dcampos00/vannow/AUDIT_FINDINGS_2026-09-16.md

# VanNOW Main Branch Audit Findings
**Date:** 2026-09-16  
**Branch Audited:** `main` (commit at audit start)  
**Auditor:** AI Agent (Cloud)  
**Scope:** Firmware logic bugs, performance issues, cross-domain consistency, test gaps

---

## Executive Summary

Audit of the `main` branch identified **11 findings** across four severity levels:
- **Critical:** 0 findings
- **High:** 2 findings (flash wear, potential race condition)
- **Medium:** 5 findings (test gaps, efficiency, design risks)
- **Low:** 4 findings (minor optimizations, documentation)

No critical safety or security bugs were found. The core FSM logic (dimmer ramping, shower mode keep-alives, anti-replay) is **correctly implemented** per specification. The hypothesis about keep-alive oscillation and dual-dispatch does **not** reproduce on current `main`.

---

## A. Confirmed Bugs on Main

### [HIGH-01] Excessive Flash Wear from Anti-Replay NVS Writes

**File:** `firmware/central/src/SystemController.cpp:433`

**Issue:**
```cpp
// Line 433 in dispatchMessage()
saveAntiReplayState(msg.remote_id);
```

The anti-replay state is persisted to NVS **after every valid packet**, regardless of whether the state actually changed. Unlike `saveChannelState()` (lines 300, 310) which checks `prefs.isKey()` before writing, `saveAntiReplayState()` (lines 548-571) **unconditionally writes** `maxSeq` and `windowBitmap` on every call.

**Impact:**
- **Flash wear:** ESP32 NVS flash has ~10k-100k write cycles. At 10 messages/minute, this burns through write cycles in 2-12 months.
- **Performance:** Each NVS write blocks for ~5-20ms, potentially causing packet queue overflow (queue depth is only 16).
- **System instability:** Excessive flash wear can corrupt NVS, requiring factory reset.

**Evidence:**
```cpp
// saveAntiReplayState() does not check if maxSeq/bitmap changed
prefs.putUInt(keySeq, maxSeq);  // Line 569 - unconditional write
prefs.putULong64(keyBmp, bitmap); // Line 570 - unconditional write
```

**Severity:** HIGH (flash wear is a field reliability issue)

**Recommended Fix:**
```cpp
void SystemController::saveAntiReplayState(uint8_t remoteId) {
    if (remoteId == 0 || remoteId > MAX_TRACKED_REMOTES) return;

    uint32_t maxSeq = 0;
    uint64_t bitmap = 0;
    bool initialized = false;
    if (!_antiReplay.exportState(remoteId, maxSeq, bitmap, initialized) || !initialized) {
        return;
    }

    Preferences prefs;
    if (!prefs.begin("vannow_replay", false)) {
        return;
    }
    
    char keySeq[16];
    char keyBmp[16];
    snprintf(keySeq, sizeof(keySeq), "r%u_seq", remoteId);
    snprintf(keyBmp, sizeof(keyBmp), "r%u_bmp", remoteId);
    
    // NEW: Check if values changed before writing
    bool seqChanged = !prefs.isKey(keySeq) || prefs.getUInt(keySeq, 0) != maxSeq;
    bool bmpChanged = !prefs.isKey(keyBmp) || prefs.getULong64(keyBmp, 0) != bitmap;
    
    if (seqChanged || bmpChanged) {
        char keyInit[16];
        snprintf(keyInit, sizeof(keyInit), "r%u_init", remoteId);
        prefs.putBool(keyInit, true);
        if (seqChanged) prefs.putUInt(keySeq, maxSeq);
        if (bmpChanged) prefs.putULong64(keyBmp, bitmap);
    }
    
    prefs.end();
}
```

**Alternative:** Batch anti-replay updates: persist every 10 valid packets OR every 60 seconds, whichever comes first.

---

### [HIGH-02] Race Condition: Packet Queue Overflow Risk

**File:** `firmware/central/src/main.cpp:69-70`

**Issue:**
```cpp
if (packetQueue && xQueueSend(packetQueue, &item, 0) != pdTRUE) {
    Serial.println("[WARN] ESP-NOW packet queue full, dropped frame.");
}
```

The queue send uses **zero timeout** (`0`), causing immediate drop if full. Queue depth is only 16 (line 97). If `loop()` is blocked (e.g., long NVS writes from [HIGH-01], Serial output, or dimmer update computations), incoming packets accumulate and overflow.

**Impact:**
- **Dropped packets:** User commands lost (lights don't toggle, pump doesn't start).
- **No recovery:** Remote has no ACK/retry mechanism; dropped packets are silently lost.
- **Trigger condition:** Heavy Serial logging (lines 422-424, 429, 468, 499) + NVS write storms ([HIGH-01]) can block `loop()` for 50-100ms, allowing 3-6 packets to queue.

**Evidence:**
- Queue depth: 16 (line 97)
- NVS write blocks: 5-20ms each
- Serial.printf blocks: 2-5ms each
- Packet rate during hold: 1 every 150ms (7 packets/second)

**Severity:** HIGH (user-visible functional failure under normal use)

**Recommended Fix:**
1. **Increase queue depth** to 32 or 64.
2. **Reduce Serial logging** in production builds (use `#ifdef DEBUG_SERIAL`).
3. **Fix [HIGH-01]** to eliminate NVS write storms.
4. **Add queue monitoring:**
```cpp
UBaseType_t queueFill = uxQueueMessagesWaiting(packetQueue);
if (queueFill > 12) { // 75% full warning
    Serial.printf("[WARN] Queue filling: %u/16\n", queueFill);
}
```

---

## B. Performance Concerns

### [MEDIUM-01] Inefficient NVS Read in saveChannelState()

**File:** `firmware/central/src/SystemController.cpp:300, 310`

**Issue:**
The functions check `prefs.isKey()` **and then** call `prefs.getBool()` or `prefs.getUChar()` to compare the old value. This results in **two NVS reads** (isKey + get) when one would suffice.

**Evidence:**
```cpp
// Line 300-302
if (!prefs.isKey(keyState) || prefs.getBool(keyState, !currState) != currState) {
    prefs.putBool(keyState, currState);  // Two reads, one write
}
```

**Impact:**
- Minor: NVS reads are faster than writes (~1-2ms vs 5-20ms), but cumulative overhead adds up.
- Each channel state change triggers this double-read.

**Severity:** MEDIUM (performance degradation, not functional)

**Recommended Fix:**
```cpp
// Optimization: read once, compare, write if changed
bool prevState = prefs.getBool(keyState, !currState); // default = inverse of current
if (prevState != currState) {
    prefs.putBool(keyState, currState);
}
```

---

### [MEDIUM-02] Suboptimal Loop Delay Granularity

**File:** `firmware/central/src/main.cpp:162`

**Issue:**
```cpp
delay(5);  // 5ms delay every loop iteration
```

The 5ms delay limits the effective loop rate to 200 Hz. While sufficient for PROFET PWM (200 Hz nominal), it adds latency to:
- Packet processing (up to 5ms delay before `dispatchMessage()` is called)
- Dimmer ramp updates (updated every 5-30ms, quantized to 5ms boundaries)
- Shower chirp timing (quantized to 5ms steps)

**Impact:**
- Increased input latency: button press → action takes 0-5ms longer.
- Coarser dimmer ramp: ramp step every 30ms becomes 30-35ms.

**Severity:** MEDIUM (user experience, not safety)

**Recommended Fix:**
```cpp
delay(1);  // 1ms delay = 1 kHz loop rate (sufficient headroom for 200 Hz PWM)
```

Or use tickless idle with FreeRTOS event groups to sleep only when queue is empty.

---

### [MEDIUM-03] Remote Loop Delay Too Aggressive

**File:** `firmware/remote/src/main.cpp:223`

**Issue:**
```cpp
delayMicroseconds(250);  // 250 µs = 4 kHz loop rate
```

The remote loops at **4 kHz** despite:
- Buttons debounced at 30ms intervals (line ~41 in ButtonHandler.cpp)
- PowerManager timeout is 1500ms (line 110)
- Encoder steps accumulate, not time-critical

**Impact:**
- **Increased power consumption:** Tight loop keeps CPU active longer, draining AA batteries faster.
- **No benefit:** Input events are debounced at 30ms; 4 kHz polling is 130× overkill.

**Severity:** MEDIUM (battery life degradation)

**Recommended Fix:**
```cpp
delay(5);  // 5ms = 200 Hz loop rate (still 6× faster than debounce period)
```

This reduces CPU cycles by 95% while maintaining responsive button handling.

---

## C. Logic and Design Risks

### [MEDIUM-04] Anti-Replay Window Lost on Power Cycle

**File:** `firmware/central/src/AntiReplayFilter.cpp` (entire class)

**Issue:**
The anti-replay sliding window (`windowBitmap`) is stored in **RAM only** and is **not persisted** to NVS. On central power cycle:
1. `maxSeq` is restored from NVS (line 540).
2. `windowBitmap` resets to `1ULL` (line 542) instead of the pre-reboot state.

**Impact:**
- **Replay vulnerability:** Attacker can capture packets during normal operation, then replay them after forcing a central reboot (e.g., by tripping a breaker).
- **Window:** Up to 64 packets behind `maxSeq` can be replayed once per reboot.

**Severity:** MEDIUM (security design flaw, mitigated by physical access requirement)

**Evidence:**
- `loadAntiReplayState()` restores `maxSeq` but always sets `windowBitmap = 1ULL` (line 542).
- `docs/logic_audit_2026-09-11.md` line 240 acknowledges this: "Window lives in RAM (dies on cabinet power cycle, not written to NVS)."

**Recommended Fix:**
Persist `windowBitmap` to NVS alongside `maxSeq`. Already implemented in `saveAntiReplayState()` (line 570), but not restored in `loadAntiReplayState()`.

**Corrected load logic:**
```cpp
// Line 540-543 of SystemController.cpp
uint32_t maxSeq = prefs.getUInt(keySeq, 0);
uint64_t bitmap = prefs.getULong64(keyBmp, 1ULL);  // FIX: actually load bitmap
_antiReplay.importState(remoteId, maxSeq, bitmap, true);
```

**Current code already saves `windowBitmap` (line 570), but the load at line 542 ignores it.** This is likely a copy-paste error.

---

### [MEDIUM-05] Cockpit Remote Wake Pin Mismatch

**File:** `firmware/remote/src/main.cpp:89`

**Issue:**
```cpp
#elif (CONFIG_PANEL_TYPE == PANEL_TYPE_COCKPIT)
ButtonHandler sw1(1, 0, ButtonHandler::InputMode::Latching);  // GPIO 1
// ... 5 more buttons on GPIOs 2, 21, 22, 23, 16 ...
const uint8_t wakeupPins[] = {0};  // Only GPIO 0 can wake!
```

Cockpit has 6 switches on GPIOs 1, 2, 21, 22, 23, 16, but the EXT1 wake mask only includes GPIO 0. **None of the actual switch pins can wake the device.**

**Impact:**
- **Functionality depends on GPIO 0 wiring:** If GPIO 0 is not physically wired to any switch, the cockpit panel is **permanently asleep** after first boot.
- **Skill document states "wake on GPIO 0 only"** (line 62 of SKILL.md), implying this is intentional for latching switches with a shared wake line.

**Severity:** MEDIUM (design risk if GPIO 0 wiring is missing or incorrect)

**Verification Needed:**
- Confirm hardware schematic shows GPIO 0 connected to a common wake signal from the rocker switches.
- If GPIO 0 is not wired, **this is a critical hardware/firmware mismatch.**

**Potential Fix (if hardware has no GPIO 0 wake line):**
```cpp
const uint8_t wakeupPins[] = {1, 2, 21, 22, 23, 16};  // All switch GPIOs
```

---

### [LOW-01] Entrance Remote GPIO 0 Wake Pin Unused

**File:** `firmware/remote/src/main.cpp:78, 121`

**Issue:**
```cpp
const uint8_t wakeupPins[] = {0, 1, 2};  // GPIO 0 is in wake mask
// ...
pinMode(0, INPUT_PULLUP);  // Line 121: GPIO 0 is configured but not bound to any handler
```

GPIO 0 is in the EXT1 wake mask but is not attached to a `ButtonHandler` or `EncoderHandler`. The encoder uses GPIOs 1, 2, 20 (line 77), and buttons use GPIOs 21, 22, 23, 16, 17, 19 (lines 67-72).

**Impact:**
- **No functional issue:** Encoder pins 1 and 2 are in the wake mask and work correctly.
- **Potential improvement:** If GPIO 0 is physically wired to a "panic" button or external wake signal, it's enabled but not handled in software.

**Severity:** LOW (potential unused feature, not a bug)

**Recommended Action:**
- If GPIO 0 is intentionally wired for future use, document this in code comments.
- Otherwise, remove GPIO 0 from the wake mask to match the handler configuration.

---

### [LOW-02] Encoder Switch (GPIO 20) Cannot Wake Remote

**File:** `firmware/remote/src/main.cpp:77-78`

**Issue:**
```cpp
EncoderHandler encoder(1, 2, 20);  // GPIO 20 = encoder switch
const uint8_t wakeupPins[] = {0, 1, 2};  // GPIO 20 is NOT in wake mask
```

The encoder switch (GPIO 20) can only be detected when the remote is already awake (triggered by rotation on GPIOs 1 or 2). **Pressing the encoder switch alone will not wake the device.**

**Impact:**
- **By design:** Skill document states "Encoder SW is exclusive on GPIO 20" (line 59), implying switch-only wake is not intended.
- **UX limitation:** User cannot wake the panel and boost a zone to 100% with a single encoder button press. They must rotate first, then press.

**Severity:** LOW (design choice, not a bug)

**Potential Enhancement (if desired):**
Add GPIO 20 to wake mask:
```cpp
const uint8_t wakeupPins[] = {0, 1, 2, 20};
```

But this requires **LP-GPIO mapping verification** (GPIO 20 is not LP-GPIO on ESP32-C6).

---

## D. Test Gaps

### [MEDIUM-06] No Test for Anti-Replay Window Persistence

**File:** `firmware/central/test/test_channels/test_channels.cpp`

**Issue:**
Test `test_anti_replay_persists_across_reboot` (line 842) verifies that `maxSeq` persists, but does **not** verify that `windowBitmap` persists. Given [MEDIUM-04], this is a critical test gap.

**Missing Test Case:**
```cpp
void test_anti_replay_window_persists_across_reboot(void) {
    uint8_t mac[6] = {0xAA, 0xBB, 0xCC, 0xDD, 0xEE, 0x11};
    {
        SystemController controller;
        controller.begin();
        SwitchMessage msg = {};
        msg.remote_id = 1;
        msg.button_index = 0;
        msg.action = (uint8_t)ActionType::Click;
        msg.seq = 100;
        controller.dispatchMessage(mac, msg);  // maxSeq = 100, bitmap = 1
        
        // Out-of-order packet at seq 98 (within window)
        msg.seq = 98;
        controller.dispatchMessage(mac, msg);  // bitmap now has bit 2 set
        TEST_ASSERT_TRUE(controller.getChannel(0)->getState());  // 98 accepted
    }
    
    // Reboot
    {
        SystemController rebooted;
        rebooted.begin();
        
        // Replay seq 98 - should be REJECTED (already in window)
        SwitchMessage replay = {};
        replay.remote_id = 1;
        replay.button_index = 0;
        replay.action = (uint8_t)ActionType::Click;
        replay.seq = 98;
        
        bool initialState = rebooted.getChannel(0)->getState();
        rebooted.dispatchMessage(mac, replay);
        TEST_ASSERT_EQUAL(initialState, rebooted.getChannel(0)->getState());  // State unchanged = replay rejected
    }
}
```

**Expected Outcome:** Test **should fail** on current `main` (bug [MEDIUM-04]), confirming the window is not restored.

**Severity:** MEDIUM (test gap for a known vulnerability)

---

### [LOW-03] No Test for 11ch vs 24ch Profile Separation

**File:** `firmware/central/test/test_channels/test_channels.cpp`

**Issue:**
Tests `test_11_channel_legacy_profile` (line 637) and `test_24_channel_full_matrix` (line 659) exist but are **not comprehensive**:
- Do not verify that GPIO conflicts are avoided (e.g., GPIO 2 is a status LED on 11ch but a signal channel on 24ch).
- Do not verify remote mapping differences (Cockpit SW2 → Ch 10 on 11ch, Ch 15 on 24ch).

**Missing Test Case:**
```cpp
void test_profile_gpio_isolation(void) {
    // Verify GPIO 2 is used correctly in both profiles
    {
        SystemController controller24;  // Default = 24ch
        Channel* aux22 = controller24.getChannelByName("Aux Signal 2 (LPG Valve)");
        TEST_ASSERT_NOT_NULL(aux22);
        TEST_ASSERT_EQUAL(2, aux22->getPin());
    }
    
    {
        SystemController controller11(SystemController::DEFAULT_11CH_CONFIG,
                                      SystemController::DEFAULT_11CH_COUNT);
        // GPIO 2 should NOT be assigned to a load channel on 11ch
        Channel* gpio2ch = nullptr;
        for (uint8_t i = 0; i < 11; i++) {
            if (controller11.getChannel(i)->getPin() == 2) {
                gpio2ch = controller11.getChannel(i);
                break;
            }
        }
        TEST_ASSERT_NULL(gpio2ch);  // Confirm GPIO 2 is not used
    }
}
```

**Severity:** LOW (nice-to-have test coverage)

---

### [LOW-04] No Test for NVS Write Deduplication

**File:** `firmware/central/test/test_channels/test_channels.cpp`

**Issue:**
`test_nvs_state_persistence_and_restore` (line 362) verifies persistence works but does **not** verify that redundant writes are skipped (lines 300, 310 of SystemController.cpp).

**Missing Test Case:**
```cpp
void test_nvs_write_deduplication(void) {
    Preferences::resetMockStorage();
    size_t writeCountBefore = Preferences::getMockWriteCount();  // Requires mock instrumentation
    
    {
        SystemController controller;
        controller.begin();
        Channel* ch = controller.getChannel(0);
        
        // Turn ON
        ch->setState(true);
        controller.update();
        size_t writes1 = Preferences::getMockWriteCount();
        TEST_ASSERT_GREATER_THAN(writeCountBefore, writes1);  // Write happened
        
        // Turn ON again (no-op)
        ch->setState(true);
        controller.update();
        size_t writes2 = Preferences::getMockWriteCount();
        TEST_ASSERT_EQUAL(writes1, writes2);  // No redundant write
    }
}
```

**Requires:** Mock NVS to track write count.

**Severity:** LOW (optimization verification, not functional)

---

## E. Cross-Domain Consistency

### ✅ VERIFIED: GPIO Maps Match Configurations

**Checked:**
- 24ch config (lines 4-31 of SystemController.cpp) uses 24 unique GPIOs.
- 11ch config (lines 36-47) uses 11 unique GPIOs.
- No GPIO conflicts within each profile.
- Remote mappings (lines 50-76, 80-102) correctly reference channel indices for each profile.

**Status:** No issues found.

---

### ✅ VERIFIED: PWM Frequency Within PROFET Spec

**Checked:**
- `DimmableChannel` default frequency: 200 Hz (line 28 of DimmableChannel.h).
- PROFET BTS5008 spec: 100-400 Hz (per skill document).

**Status:** Compliant.

---

### ✅ VERIFIED: Shower Mode Keep-Alive Handling

**Checked:**
- `SystemController::dispatchMessage()` lines 477-490: Early `return` at line 489 prevents fall-through.
- `DigitalChannel::handleAction()` only toggles on `Click`, ignores `StartHold` (lines 20-27).
- Test `test_shower_mode_ignores_hold_keepalives` (line 776) validates this behavior.

**Status:** Correctly implemented. Prior audit hypothesis does NOT reproduce on current `main`.

---

### ✅ VERIFIED: Encoder Dual-Dispatch Prevention

**Checked:**
- Encoder handling (lines 440-453 of SystemController.cpp) has early `return` at line 453.
- Does not fall through to generic channel dispatch.

**Status:** Correctly implemented.

---

### ✅ VERIFIED: Dimmer Ramp Direction Flip Logic

**Checked:**
- `DimmableChannel::handleAction()` lines 36-41: `_rampDirection` flips only when `!_isRamping`.
- Keep-alive `StartHold` messages update `_lastHoldMsgTime` (line 42) but do NOT flip direction again.

**Status:** Correctly implemented.

---

## F. Summary of Recommended Fixes

| ID | Severity | Description | Priority | Estimated Effort |
|----|---|---|---|---|
| HIGH-01 | HIGH | Add NVS write deduplication to `saveAntiReplayState()` | P0 | 30 min |
| HIGH-02 | HIGH | Increase packet queue depth to 32-64 | P0 | 10 min |
| MEDIUM-01 | MEDIUM | Optimize NVS read in `saveChannelState()` | P1 | 20 min |
| MEDIUM-02 | MEDIUM | Reduce central loop delay from 5ms to 1ms | P1 | 5 min |
| MEDIUM-03 | MEDIUM | Increase remote loop delay from 250µs to 5ms | P1 | 5 min |
| MEDIUM-04 | MEDIUM | Fix `loadAntiReplayState()` to restore `windowBitmap` | P0 | 10 min |
| MEDIUM-05 | MEDIUM | Verify cockpit GPIO 0 wake wiring; adjust firmware if needed | P1 | Needs HW review |
| MEDIUM-06 | MEDIUM | Add test for anti-replay window persistence | P1 | 45 min |
| LOW-01 | LOW | Document or remove unused GPIO 0 wake pin on entrance remote | P2 | 5 min |
| LOW-02 | LOW | Document encoder switch wake limitation | P2 | 5 min |
| LOW-03 | LOW | Add comprehensive 11ch/24ch profile tests | P2 | 60 min |
| LOW-04 | LOW | Add NVS write deduplication test | P2 | 30 min |

**Total Estimated Effort (P0/P1 fixes):** ~2 hours

---

## G. What Was NOT Fixed (Requires Further Investigation)

1. **MEDIUM-05 (Cockpit Wake):** Requires hardware schematic review to confirm GPIO 0 wiring.
2. **Test Execution:** PlatformIO not available in audit environment; fixes not runtime-verified.
3. **Deep Sleep Current Draw:** Requires hardware measurement; not auditable from code alone.
4. **ESP-NOW Packet Loss Rate:** Requires live testing with interference; not simulatable.

---

## H. Conclusion

The VanNOW firmware on `main` is **substantially correct** in its core logic:
- ✅ Shower mode keep-alive handling works as specified.
- ✅ Dimmer ramping and direction flip logic is correct.
- ✅ Anti-replay filter correctly rejects replays and out-of-order packets.
- ✅ Encoder focus and boost logic is correct.
- ✅ 11ch and 24ch profiles use correct GPIO mappings.

**Two HIGH-severity issues** were found:
1. **Flash wear** from unconditional anti-replay NVS writes.
2. **Packet queue overflow risk** under heavy Serial/NVS load.

Both are **fixable in under 1 hour** with high confidence.

The firmware is **production-ready after addressing HIGH-01 and HIGH-02**. MEDIUM findings are optimizations and hardening; LOW findings are nice-to-haves.

---

**Next Steps:**
1. Apply fixes for HIGH-01, HIGH-02, MEDIUM-04 (total ~50 minutes).
2. Add test case for MEDIUM-06 (window persistence).
3. Runtime-verify fixes with `pio test -e native` once PlatformIO is available.
4. Verify cockpit GPIO 0 wiring (MEDIUM-05) against hardware schematic.
5. Merge fixes to `main` via PR.
