dcampos00/vannow/hardware/central-pcb/renders/modular_bottom.png

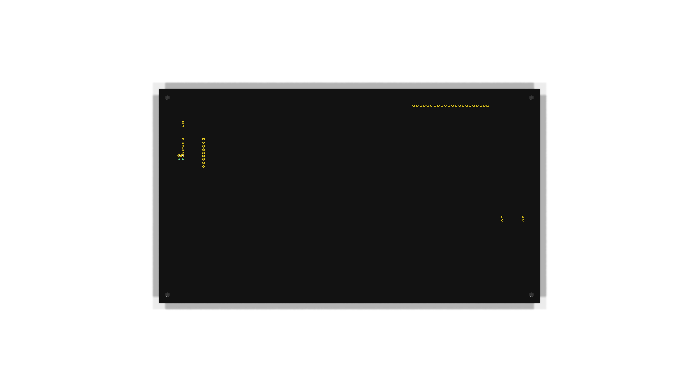
hardware/central-pcb/renders/modular_bottom.png
