dcampos00/vannow/hardware/central-pcb/renders/modular_silkscreen.png

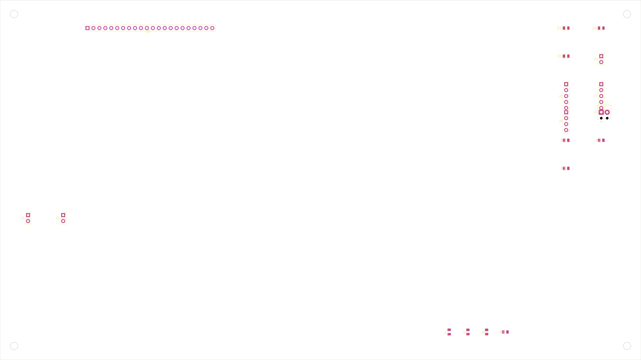
hardware/central-pcb/renders/modular_silkscreen.png
