dcampos00/vannow/hardware/central-pcb/renders/modular_top.png

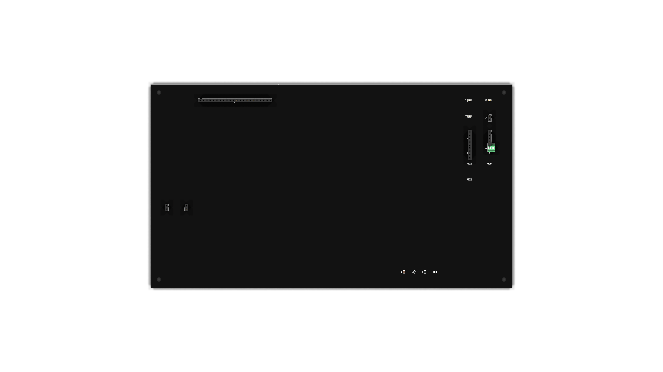
hardware/central-pcb/renders/modular_top.png
