dcampos00/vannow/hardware/central-pcb/renders/profet_24ch/profet_24ch_isometric.png

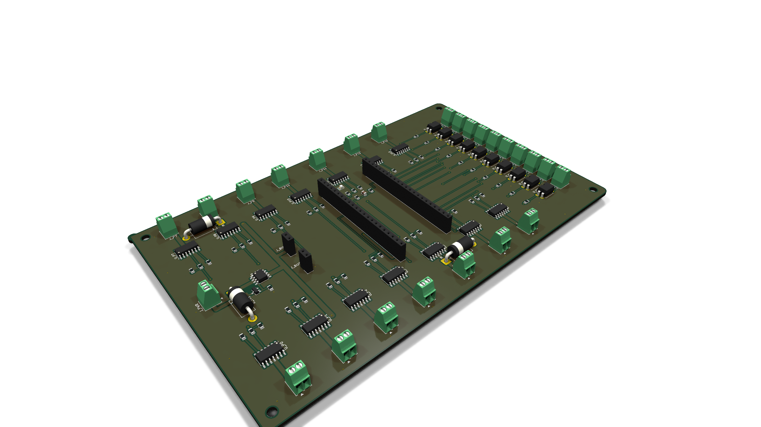
hardware/central-pcb/renders/profet_24ch/profet_24ch_isometric.png
