dcampos00/vannow/hardware/central-pcb/renders/profet_24ch/profet_24ch_top.png

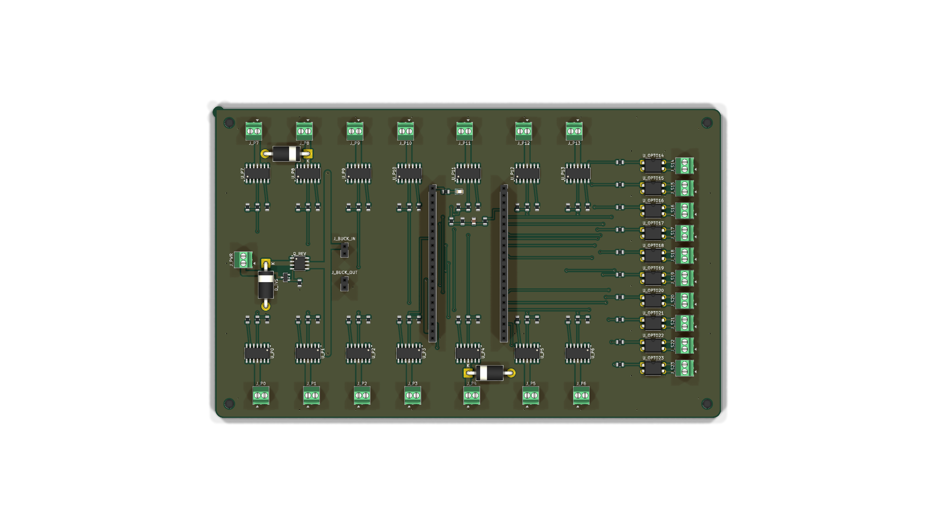
hardware/central-pcb/renders/profet_24ch/profet_24ch_top.png
