dcampos00/vannow/hardware/central-pcb/renders/profet_bottom.png

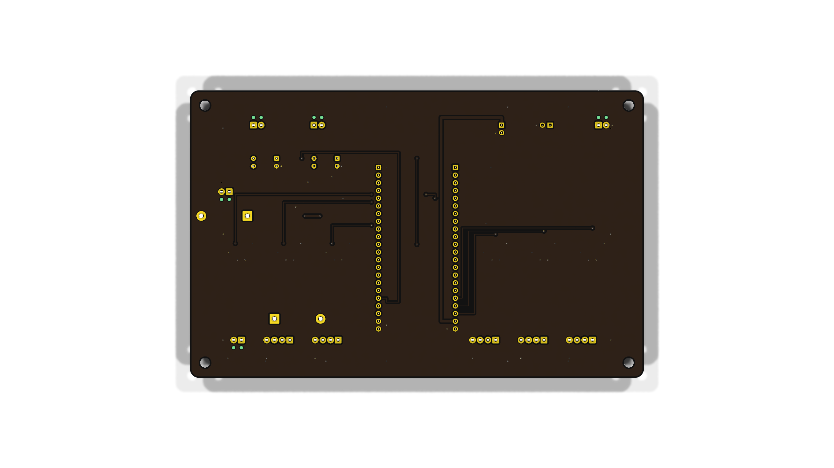
hardware/central-pcb/renders/profet_bottom.png
