dcampos00/vannow/hardware/cockpit-pcb/renders/cockpit_bottom.png

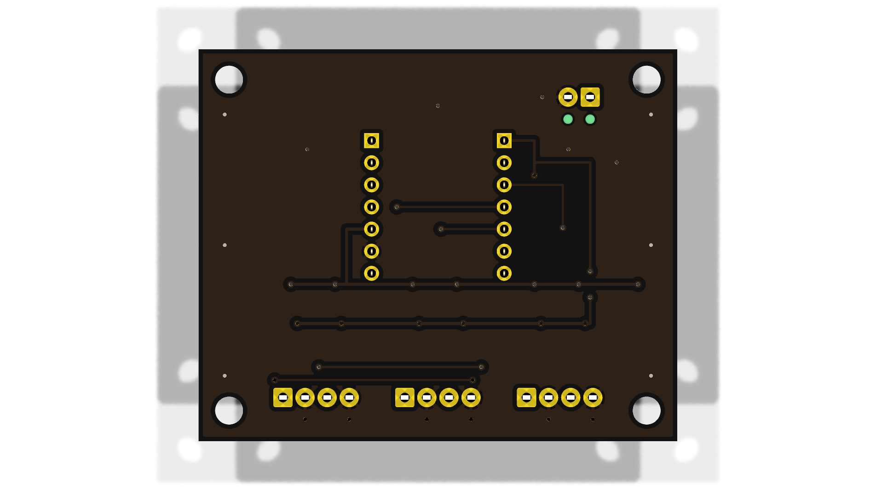
hardware/cockpit-pcb/renders/cockpit_bottom.png
