dcampos00/vannow/hardware/cockpit-pcb/renders/cockpit_isometric.png

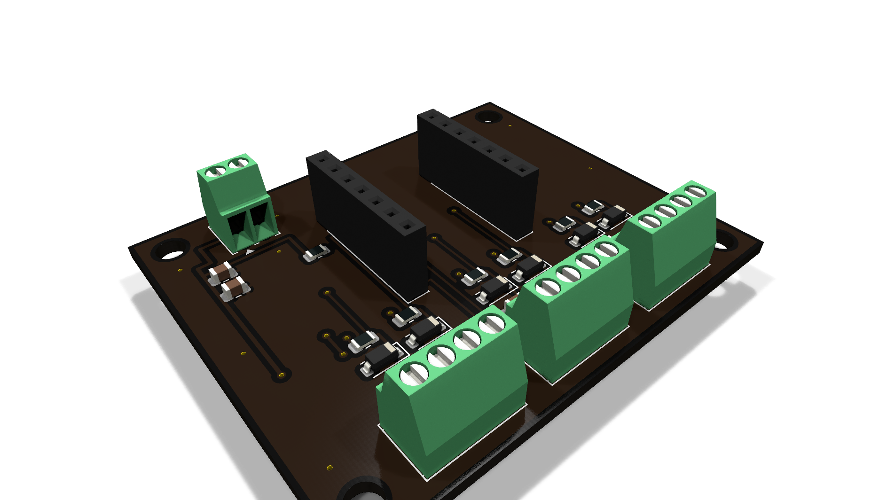
hardware/cockpit-pcb/renders/cockpit_isometric.png
