dcampos00/vannow/hardware/cockpit-pcb/renders/cockpit_top.png

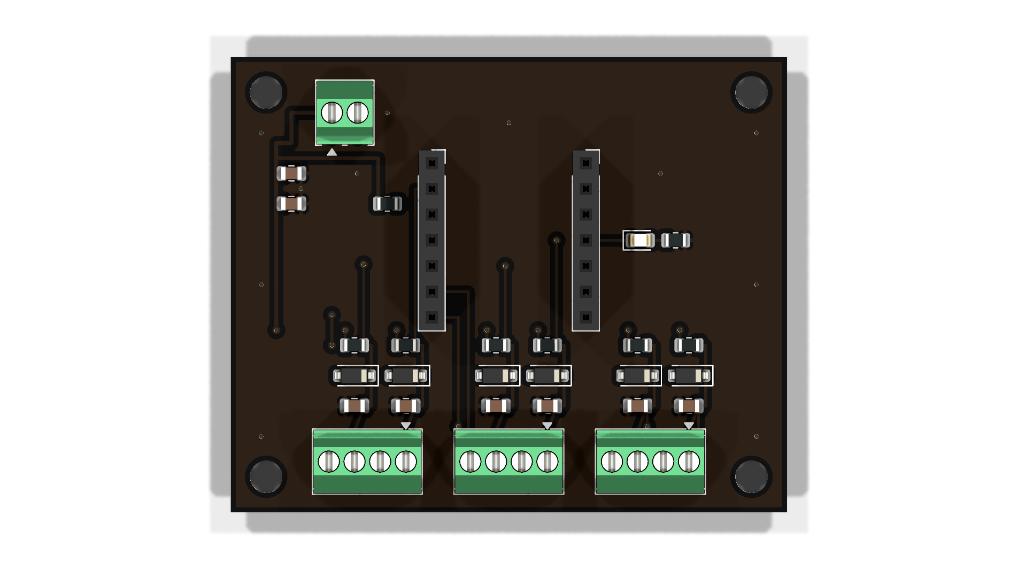
hardware/cockpit-pcb/renders/cockpit_top.png
