dcampos00/vannow/hardware/enclosures/renders/central_24ch_enclosure_base_render.png

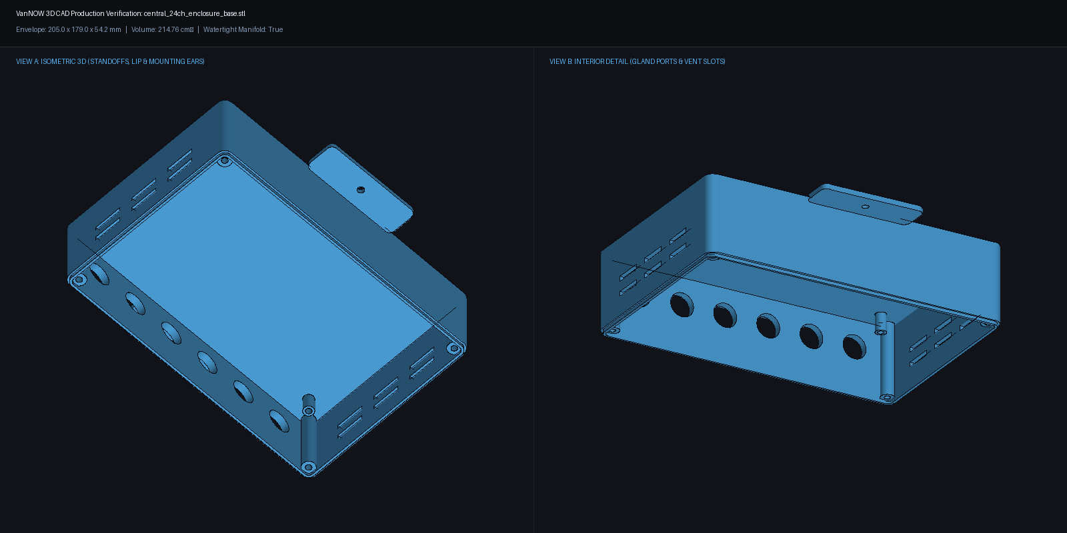
hardware/enclosures/renders/central_24ch_enclosure_base_render.png
