dcampos00/vannow/hardware/enclosures/renders/central_24ch_enclosure_lid_render.png

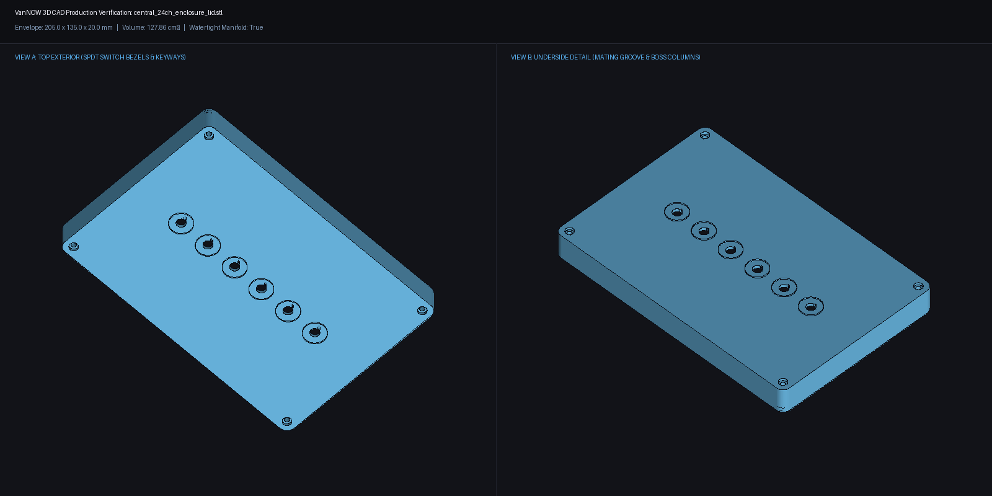
hardware/enclosures/renders/central_24ch_enclosure_lid_render.png
