dcampos00/vannow/hardware/enclosures/renders/cockpit_enclosure_base_render.png

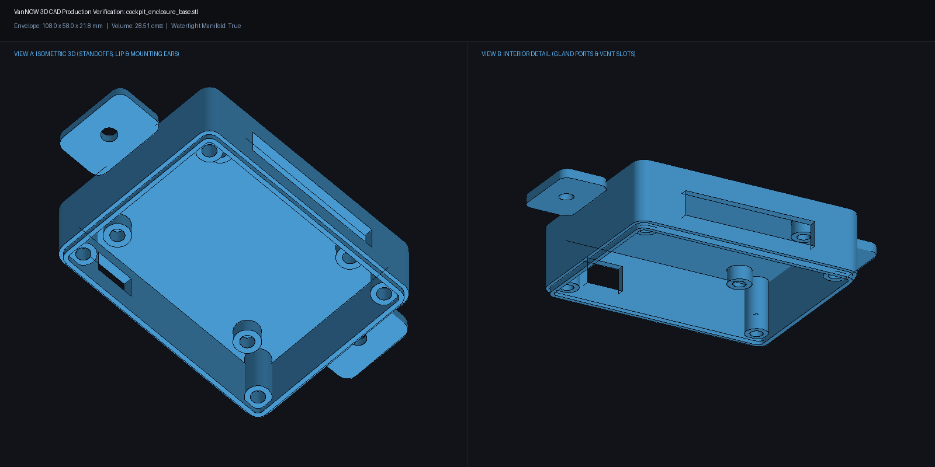
hardware/enclosures/renders/cockpit_enclosure_base_render.png
