dcampos00/vannow/hardware/enclosures/renders/remote_enclosure_body_render.png

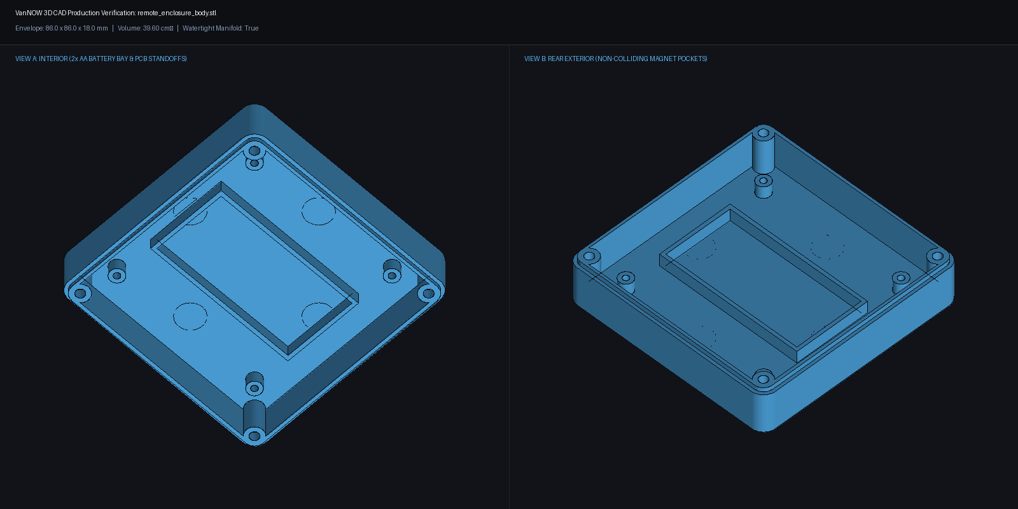
hardware/enclosures/renders/remote_enclosure_body_render.png
