dcampos00/vannow/hardware/enclosures/renders/remote_enclosure_faceplate_render.png

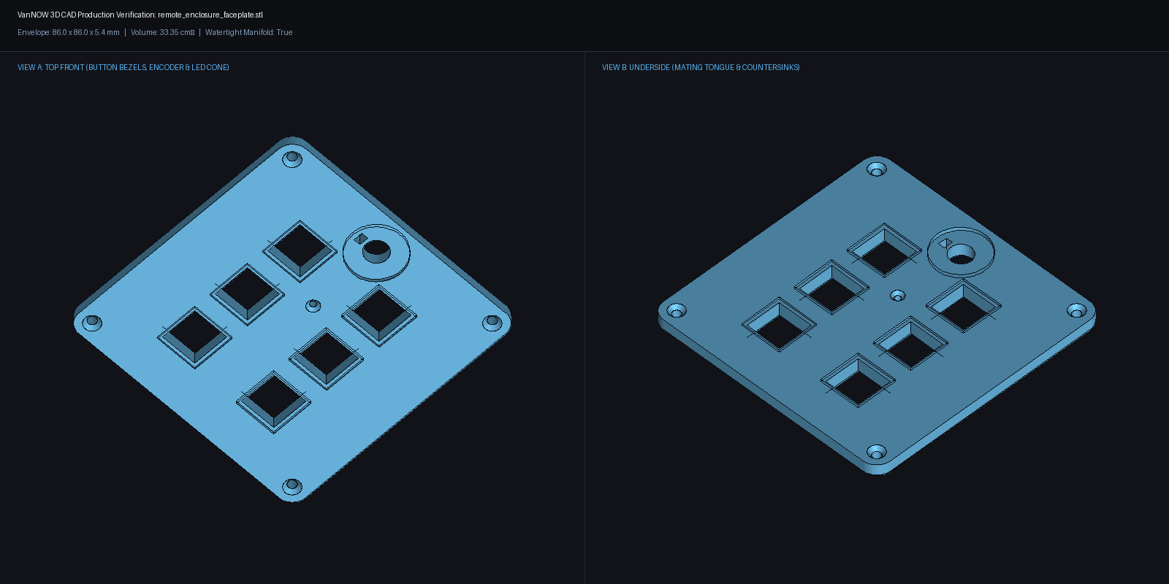
hardware/enclosures/renders/remote_enclosure_faceplate_render.png
