dcampos00/vannow/hardware/entrance-remote-pcb/renders/entrance_remote_bottom.png

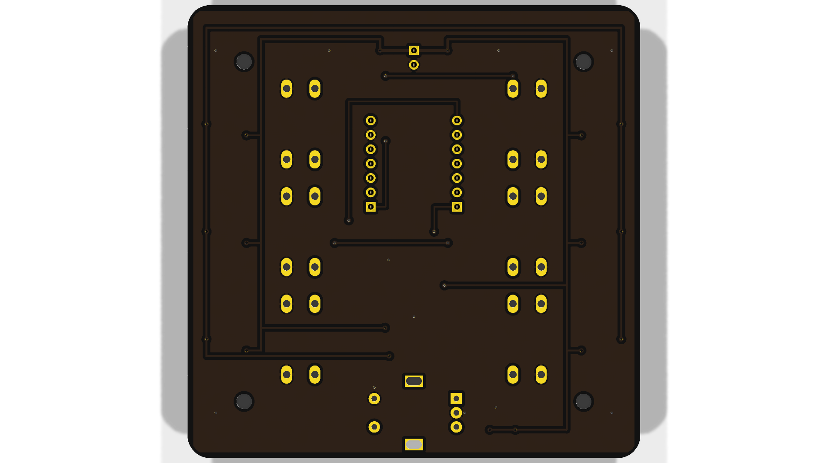
hardware/entrance-remote-pcb/renders/entrance_remote_bottom.png
