dcampos00/vannow/hardware/entrance-remote-pcb/renders/entrance_remote_isometric.png

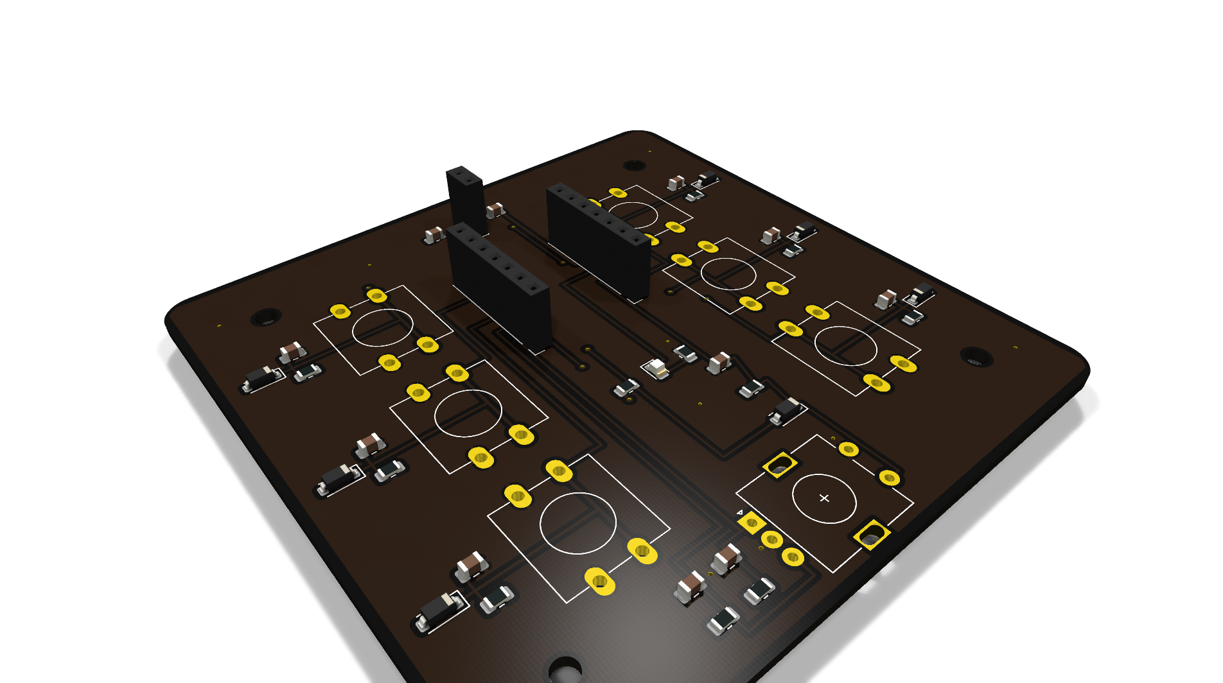
hardware/entrance-remote-pcb/renders/entrance_remote_isometric.png
