dcampos00/vannow/hardware/entrance-remote-pcb/renders/entrance_remote_top.png

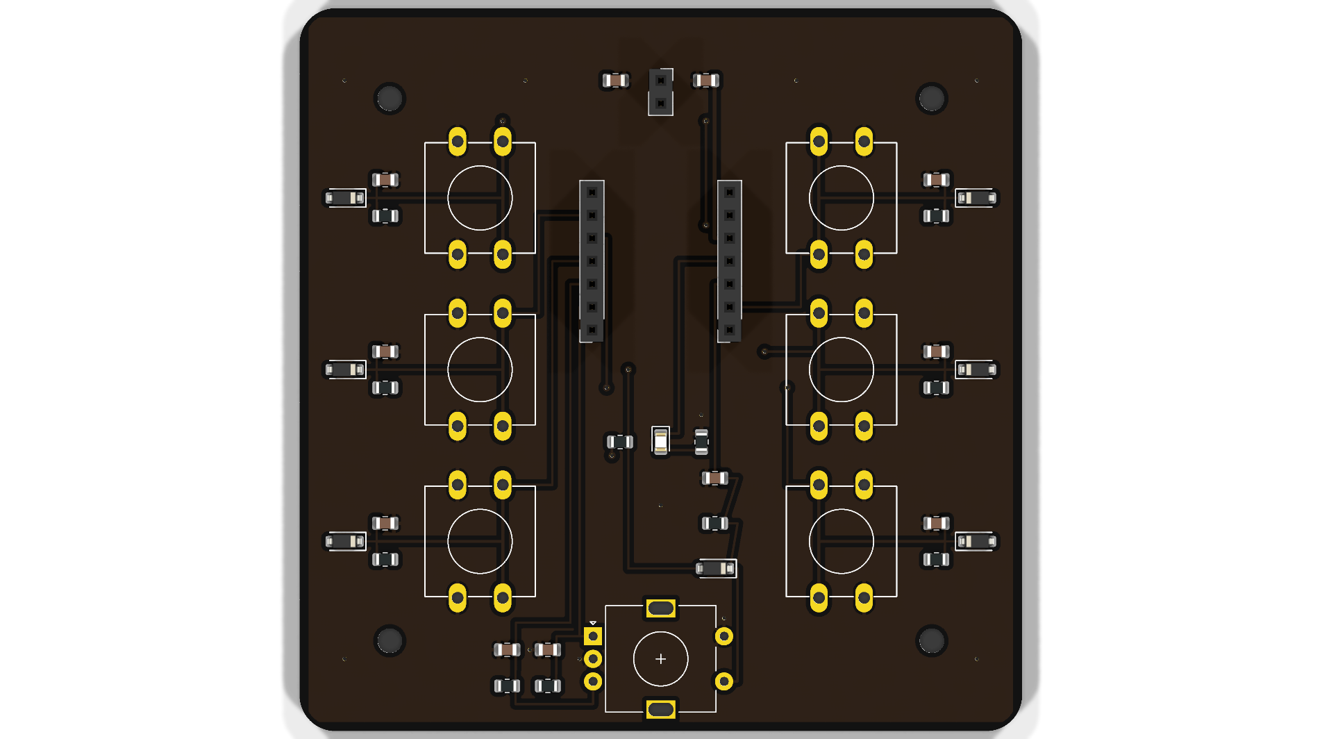
hardware/entrance-remote-pcb/renders/entrance_remote_top.png
