dcampos00/vannow/firmware/remote/src/RemoteSender.cpp

#include "RemoteSender.h"
#include <Preferences.h>

// Define static members
volatile bool RemoteSender::_messageSent = false;
volatile bool RemoteSender::_deliverySuccess = false;

#ifdef ARDUINO_ARCH_ESP32
RTC_DATA_ATTR uint32_t msgSequenceNumber = 0;
#else
static uint32_t msgSequenceNumber = 0;
#endif

RemoteSender::RemoteSender(uint8_t remoteId, const uint8_t* targetMac, uint8_t batteryPin)
    : _remoteId(remoteId), _batteryPin(batteryPin) {
    memcpy(_targetMac, targetMac, 6);
}

void RemoteSender::OnDataSent(const wifi_tx_info_t *tx_info, esp_now_send_status_t status) {
    _deliverySuccess = (status == ESP_NOW_SEND_SUCCESS);
    _messageSent = true;
}

bool RemoteSender::begin(const uint8_t* customMac) {
    if (msgSequenceNumber == 0) {
        Preferences prefs;
        if (prefs.begin("vannow_seq", true)) {
            msgSequenceNumber = prefs.getUInt("seq", 0);
            prefs.end();
        }
    }

    // Initialize battery reading pin if assigned
    if (_batteryPin != 255) {
        pinMode(_batteryPin, INPUT);
    }

    // Initialize wireless manager with optional provisioned MAC
    if (!_wireless.begin(customMac)) {
        Serial.println("Error initializing wireless manager");
        return false;
    }

    // Register callback for data transmission status
    if (!_wireless.registerSendCallback(OnDataSent)) {
        Serial.println("Error registering send callback");
        return false;
    }

    // Add Central as a peer with LMK encryption
    const uint8_t ESP_NOW_LMK[16] = {0x01, 0x02, 0x03, 0x04, 0x05, 0x06, 0x07, 0x08, 0x09, 0x0A, 0x0B, 0x0C, 0x0D, 0x0E, 0x0F, 0x10};
    if (!_wireless.addPeer(_targetMac, ESP_NOW_LMK)) {
        Serial.println("Error adding Central peer");
        return false;
    }

    return true;
}

float RemoteSender::readBatteryVoltage() {
    if (_batteryPin == 255) {
        return 3.0f; // Default nominal 2x AA battery voltage
    }
    int raw = analogRead(_batteryPin);
    // Seeed Studio XIAO ESP32-C6 defaults to 12-bit ADC (0-4095) with ~3.3V reference
    float adcVoltage = (raw / 4095.0f) * 3.3f;
    float batteryVoltage = adcVoltage * 2.0f; // 1:1 divisor (100k + 100k)
    if (raw <= 0 || batteryVoltage < 0.3f) return 0.0f;
    return batteryVoltage;
}

bool RemoteSender::send(ActionType action, uint8_t buttonIndex, int8_t rotationSteps) {
    SwitchMessage msg;
    msg.remote_id = _remoteId;
    msg.button_index = buttonIndex;
    msg.action = (uint8_t)action;
    msg.rotation_steps = rotationSteps;
    msg.battery_voltage = readBatteryVoltage();
    msg.seq = ++msgSequenceNumber;

    Serial.printf("Sending payload: Remote %d | Btn %d | Act %d | Steps %d | Bat %.2fV\n",
                  msg.remote_id, msg.button_index, msg.action, msg.rotation_steps, msg.battery_voltage);

    _messageSent = false;
    if (!_wireless.sendPayload(_targetMac, (uint8_t *)&msg, sizeof(msg))) {
        Serial.println("Error triggering ESP-NOW transmission.");
        return false;
    }

    // Await delivery status confirmation (timeout 200ms)
    uint32_t startWait = millis();
    while (!_messageSent && (millis() - startWait < 200)) {
        delay(1);
    }

    bool delivered = _messageSent && _deliverySuccess;
    _messageSent = false;
    persistSequence();
    return delivered;
}

void RemoteSender::persistSequence() {
    if (msgSequenceNumber == 0) {
        return;
    }
    Preferences prefs;
    if (!prefs.begin("vannow_seq", false)) {
        return;
    }
    prefs.putUInt("seq", msgSequenceNumber);
    prefs.end();
}
